Byvm815/Dactyl-APM/固件-Firmware/dactyl_apm/5x6v6a3/5x6v6a3.c

/* Copyright 2021 Seth Bonner <fl3tching101@gmail.com>
 *
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
 * You should have received a copy of the GNU General Public License
 * along with this program.  If not, see <http://www.gnu.org/licenses/>.
 */

#include "5x6v6a3.h"

//uf2boot has a jump function
/*
#define MAGIC_BOOT 0x544F4F42UL
#define MAGIC_REG *(volatile uint32_t*)0x20004000
void bootloader_jump_qmk_reboot(void) {
  MAGIC_REG = MAGIC_BOOT;
  NVIC_SystemReset();
}
*/
